PiStorm/pistorm32-lite-hardware/JLCPCB/pictures/bom check.png

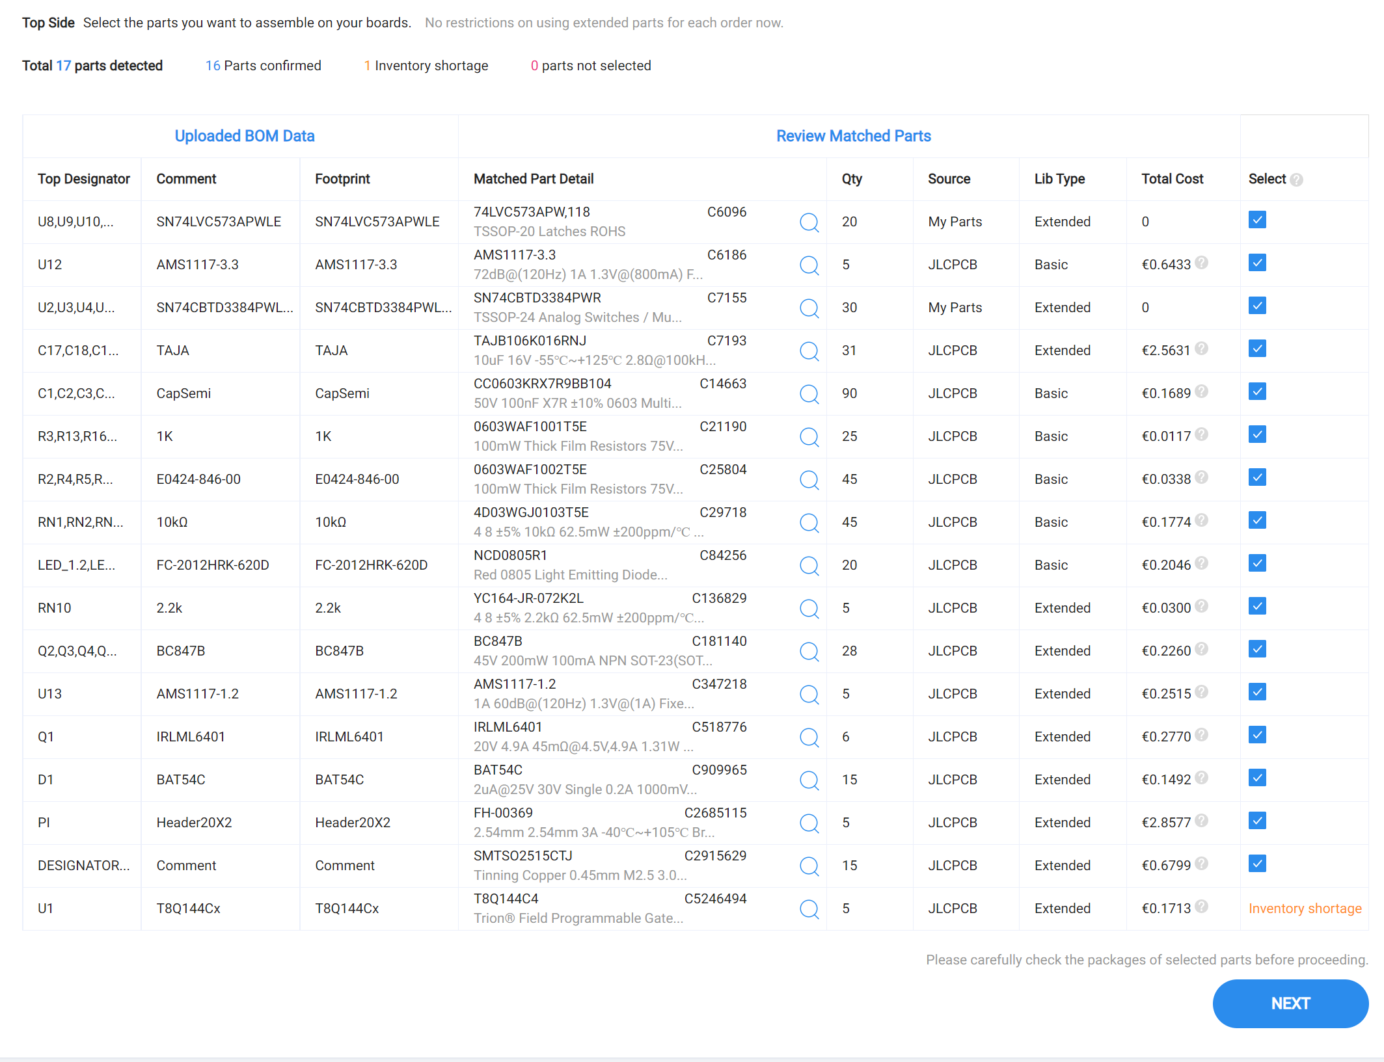
JLCPCB/pictures/bom check.png
