PiStorm/pistorm32-lite-hardware/JLCPCB/pictures/bom_cpl.png

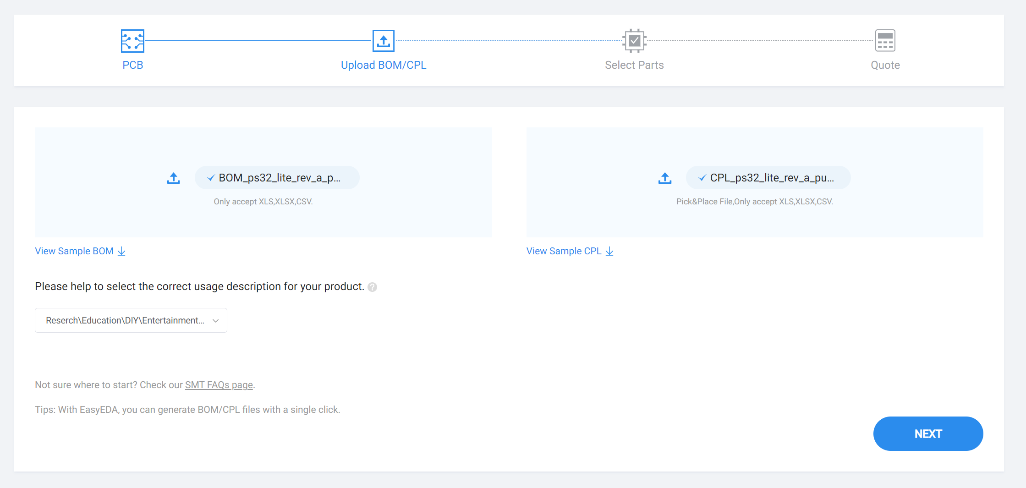
JLCPCB/pictures/bom_cpl.png
