PiStorm/pistorm32-lite-hardware/JLCPCB/pictures/remove order number.png

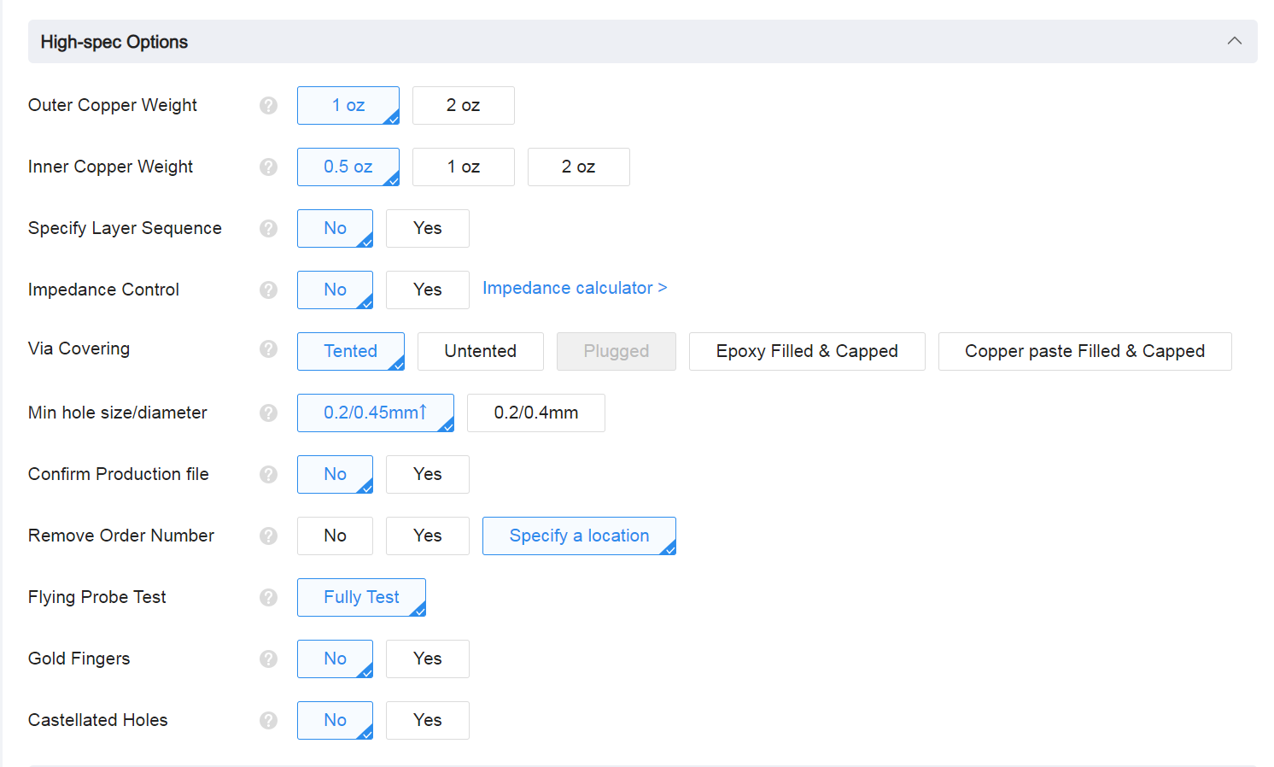
JLCPCB/pictures/remove order number.png
