PiStorm/pistorm32-lite-hardware/JLCPCB/pictures/assembly check.png

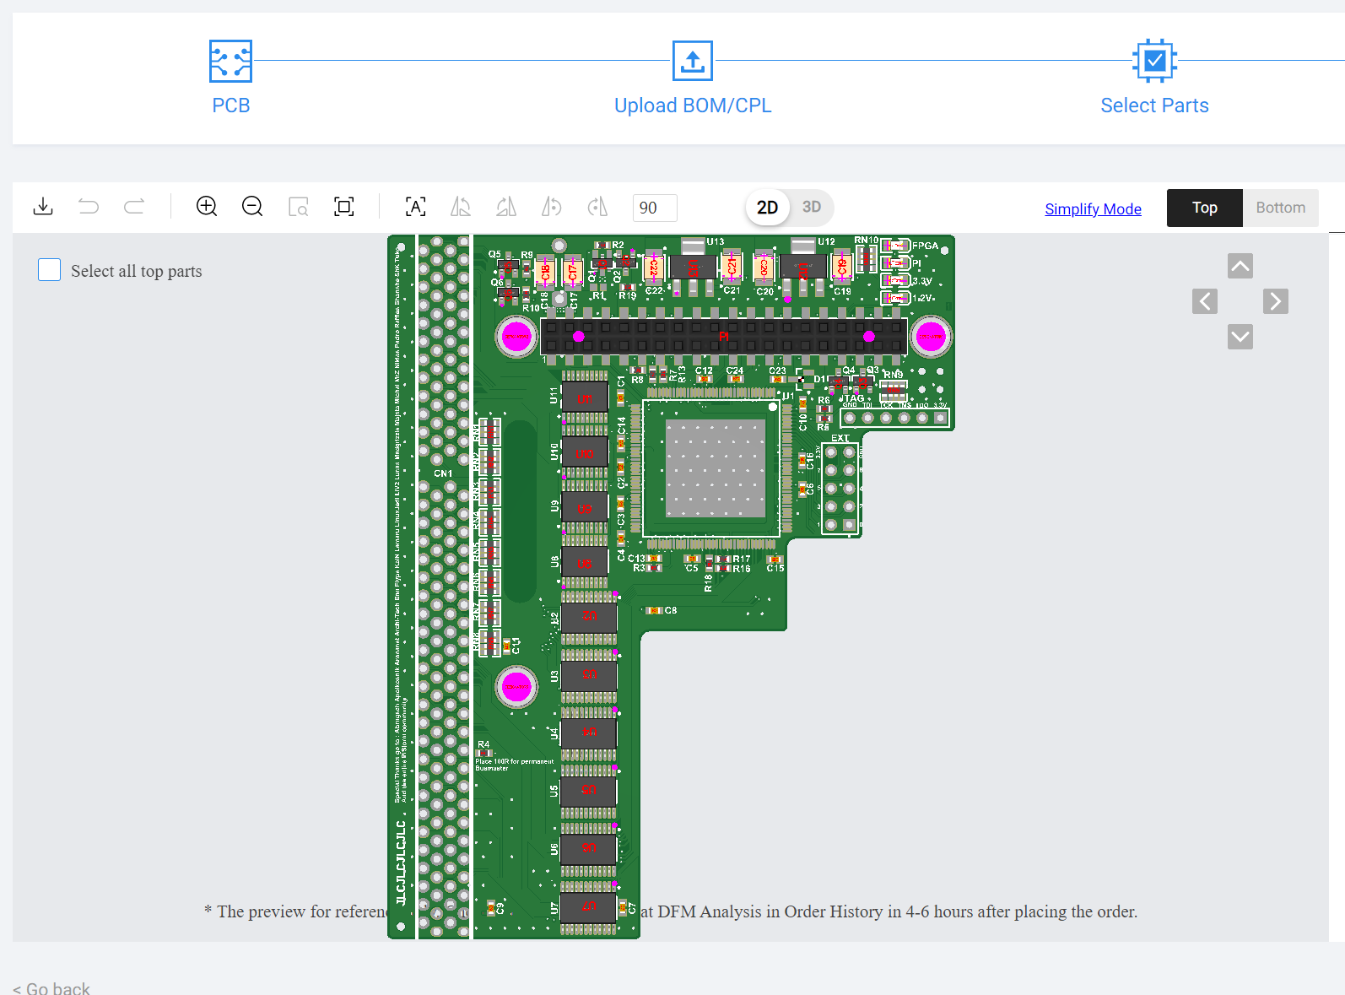
JLCPCB/pictures/assembly check.png
