PiStorm/pistorm32-lite-hardware/JLCPCB/pictures/assembly tooling holes.png

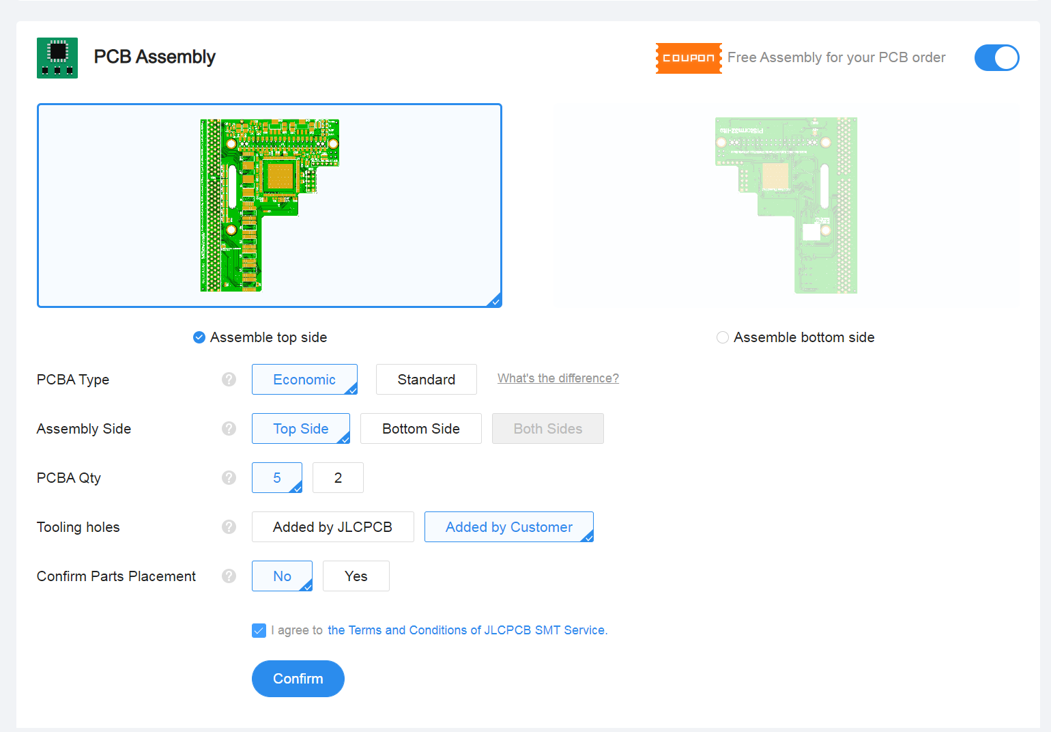
JLCPCB/pictures/assembly tooling holes.png
